andbrandt/rc-sim-timer/arduino/RcSimTimer/SimulatorReflex.hpp

#ifndef SimulatorReflex_h
#define SimulatorReflex_h

#include "Simulator.hpp"

class SimulatorReflex:public Simulator {
  public:
    void Restart();
    void Block();
    void UnBlock();
    void EasyAircraft();
    void AcroAircraft();
};
#endif
